etet100/cnc_pendant/pcb/main_nodemcu/export/g9.png

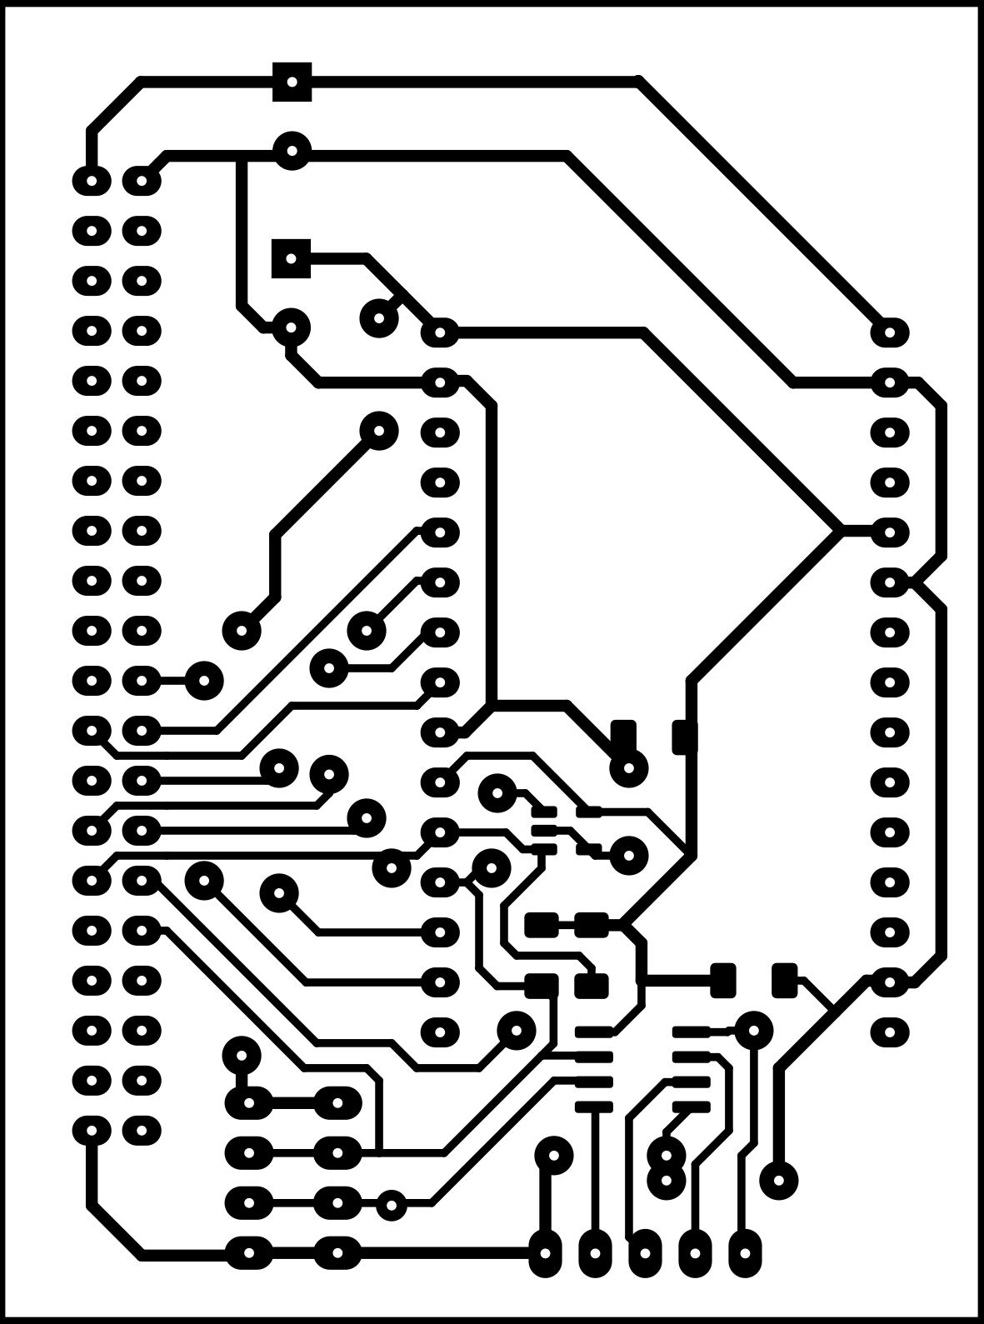
pcb/main_nodemcu/export/g9.png
