etet100/cnc_pendant/pcb/main_nodemcu/export/g39.png

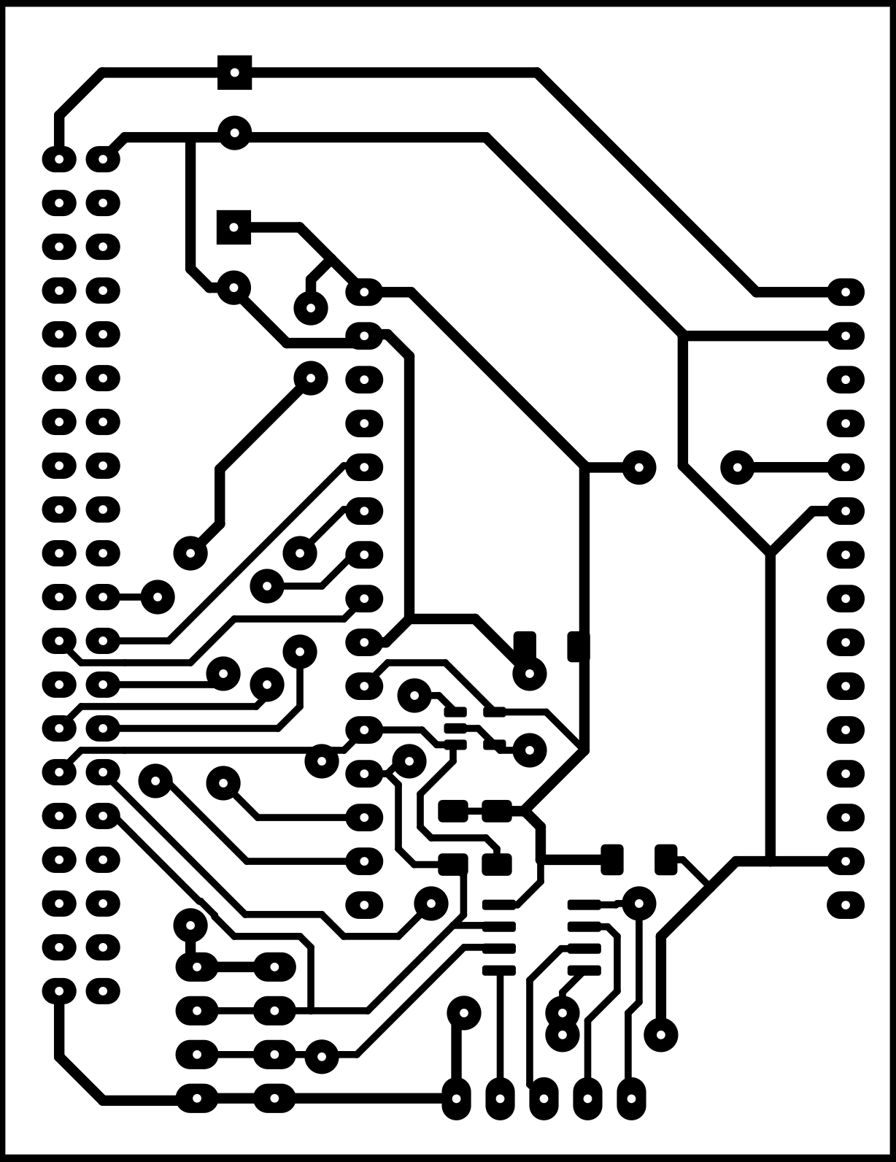
pcb/main_nodemcu/export/g39.png
