etet100/cnc_pendant/pcb/main_nodemcu/export/main-B_Cu.png

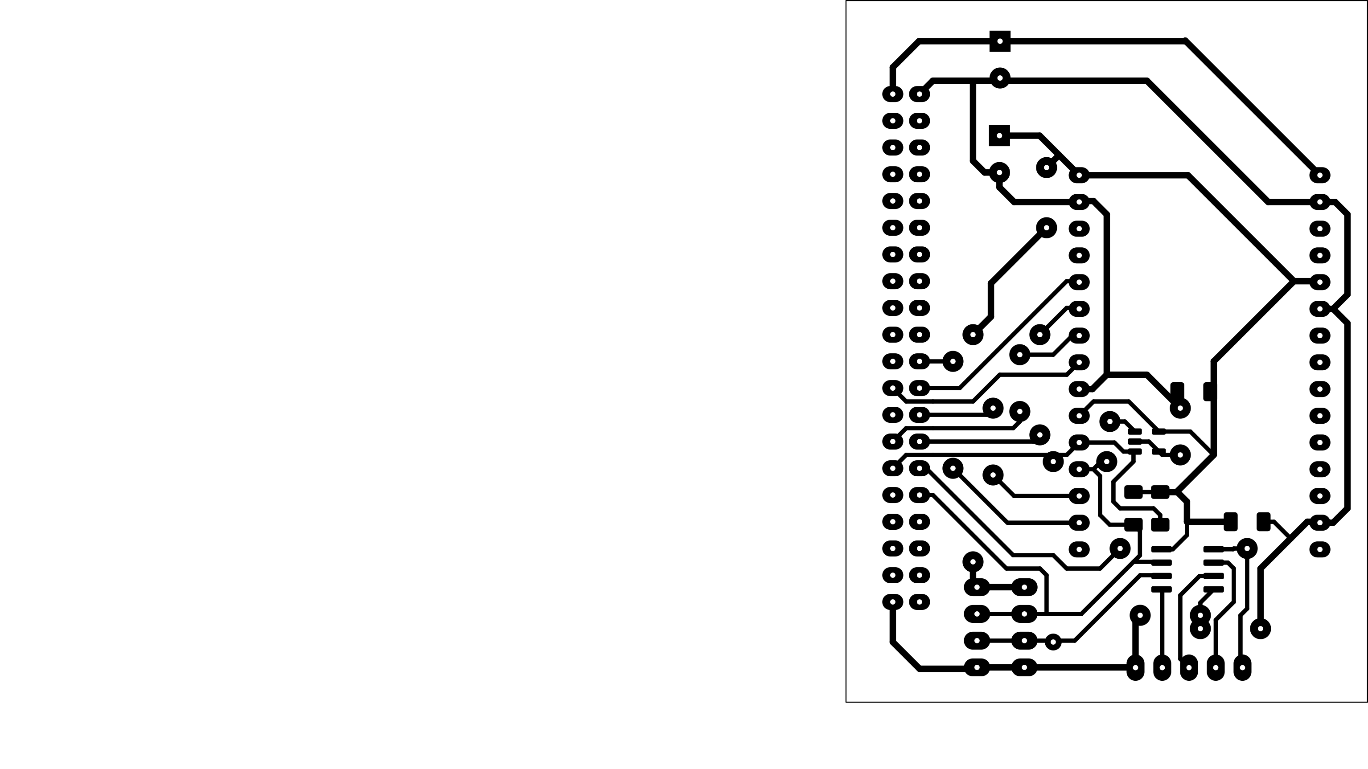
pcb/main_nodemcu/export/main-B_Cu.png
