etet100/cnc_pendant/pcb/main_v2/export/g13.png

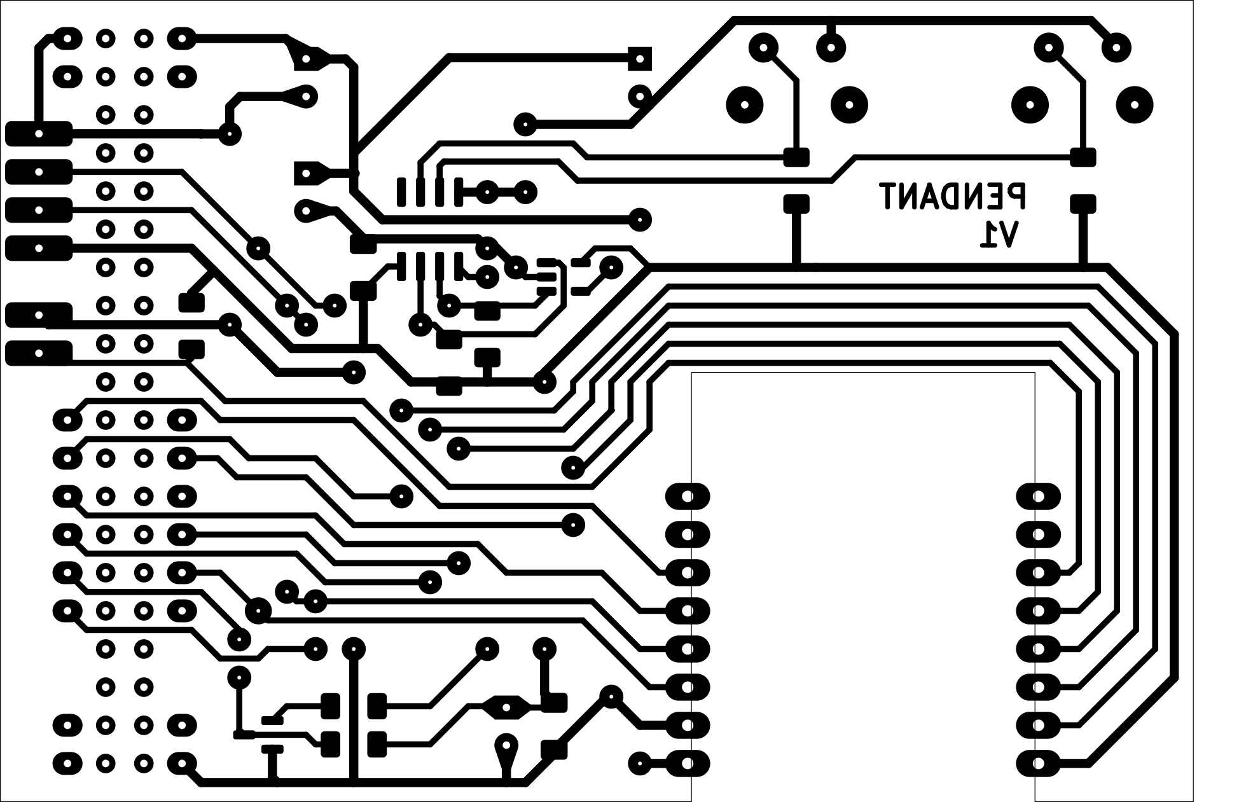
pcb/main_v2/export/g13.png
