etet100/cnc_pendant/include/state.h

#ifndef STATE_H
#define STATE_H

#include <stdint.h>
#include "communication.h"
#include "globals.h"

class State
{
    public:
        State();
        float getPos(Axis axis);
        Axis getSelectedAxis();
        uint8_t getMachineState();
        void setPos(Axis axis, float value);
        void setSelectedAxis(Axis axis);
        void fillStateMessage(StateMessage& msg);
        void setMachineState(uint8_t state);
        bool isAxisSelected(Axis axis);
        void triggerUpdatedEvent();

    private:
        float pos[3] = { 0, 0, 0 };
        uint8_t machineState = 0;
        CommunicationMode mode = CommunicationMode::NONE;
        Axis selectedAxis = Axis::None;
};

extern State state;

#endif // STATE_H
