etet100/cnc_pendant/src/state.cpp

#include "state.h"
#include "globals.h"

State::State() {
}

float State::getPos(Axis axis) {
    return pos[(int) axis];
}

Axis State::getSelectedAxis() {
    return selectedAxis;
}

uint8_t State::getMachineState() {
    return machineState;
}

bool State::isAxisSelected(Axis axis) {
    return selectedAxis == axis;
}

void State::triggerUpdatedEvent() {
    eventManager.queueEvent(EventType::StateChanged, 0);
}

void State::setPos(Axis axis, float value) {
    pos[(int)axis] = value;
}

void State::setSelectedAxis(Axis axis) {
    selectedAxis = axis;
}

void State::fillStateMessage(StateMessage &msg) {
    msg.header.start = 0xAA55;
    msg.header.size = sizeof(StateMessage);
    msg.header.type = (uint8_t) PacketType::STATE;
    msg.x = pos[(int) Axis::X];
    msg.y = pos[(int) Axis::Y];
    msg.z = pos[(int) Axis::Z];
    msg.selectedAxis = (uint8_t) selectedAxis;
    msg.mode = mode;
}

void State::setMachineState(uint8_t state) {
    this->machineState = state;
}

State state;
