etet100/cnc_pendant/include/buttons.h

#ifndef BUTTONS_H_
#define BUTTONS_H_

#include <Wire.h>
#include <PCA9536D.h>
#include "globals.h"

class Buttons {
    public:
        Buttons(PCA9536& pca9536d);
        void begin();
        void loop();
        bool isTopPressed();
        bool isBottomPressed();
        bool isWheelPressed();
        void onWheelPressed(Callback callback);

    private:
        PCA9536& pca9536d;
        uint8_t regs;
        bool wheel;
        Callback wheelPressedCallback;
};

#endif // BUTTONS_H_
