etet100/cnc_pendant/include/images.h

#ifndef H_IMAGES
#define H_IMAGES
#pragma once

struct ImageSize {
 uint16_t width;
 uint16_t height;
 uint16_t size;
};

#include "images/alive.h" // alive.png
#include "images/btn_home.h" // btn_home.png
#include "images/btn_pause.h" // btn_pause.png
#include "images/btn_power.h" // btn_power.png
#include "images/btn_reset.h" // btn_reset.png
#include "images/btn_settings.h" // btn_settings.png
#include "images/btn_spindle.h" // btn_spindle.png
#include "images/btn_start.h" // btn_start.png
#include "images/btn_stop.h" // btn_stop.png
#include "images/wifi.h" // wifi.png
#include "images/logo00.h" // logo00.png
#include "images/logo01.h" // logo01.png
#include "images/logo02.h" // logo02.png
#include "images/logo03.h" // logo03.png
#include "images/logo04.h" // logo04.png
#include "images/logo05.h" // logo05.png
#include "images/logo10.h" // logo10.png
#include "images/logo11.h" // logo11.png
#include "images/logo12.h" // logo12.png
#include "images/logo13.h" // logo13.png
#include "images/logo14.h" // logo14.png
#include "images/logo15.h" // logo15.png
#include "images/logo20.h" // logo20.png
#include "images/logo21.h" // logo21.png
#include "images/logo22.h" // logo22.png
#include "images/logo23.h" // logo23.png
#include "images/logo24.h" // logo24.png
#include "images/logo25.h" // logo25.png
#include "images/logo30.h" // logo30.png
#include "images/logo31.h" // logo31.png
#include "images/logo32.h" // logo32.png
#include "images/logo33.h" // logo33.png
#include "images/logo34.h" // logo34.png
#include "images/logo35.h" // logo35.png
#include "images/logo40.h" // logo40.png
#include "images/logo41.h" // logo41.png
#include "images/logo42.h" // logo42.png
#include "images/logo43.h" // logo43.png
#include "images/logo44.h" // logo44.png
#include "images/logo45.h" // logo45.png
#include "images/logo50.h" // logo50.png
#include "images/logo51.h" // logo51.png
#include "images/logo52.h" // logo52.png
#include "images/logo53.h" // logo53.png
#include "images/logo54.h" // logo54.png
#include "images/logo55.h" // logo55.png

#endif
